avpanasyuk/ElectricPanelMeter/LTspace/Draft1.asc

C1: cap; 0.1µF
C2: cap; 10µF
C3: cap; 2.2nF
R1: res; 6.8k
R2: res; 1.2k
R3: res; 39k
R4: res; 51k
R5: res; 10k
R6: res; 100k
V1: voltage; SINE(0 1 60); AC 1 0
Named nets: 0, Vout, Vsw
.ac list 60Hz
;tran 0 1ms 0ms 1us
